a3-audio/a3-system/a3mix/python/mic.py

# This file is a part of A³Pandemic. License is GPLv3: https://github.com/ambisonics-audio-association/Ambijockey/blob/main/COPYING
# © Copyright 2021-2022 Patric Schmitz, Raphael Eismann, Jendrik Bradaczek
#!/usr/bin/python

import sys
import math
import time
import argparse
import serial  # pySerial https://pyserial.readthedocs.io/
import numpy as np

import board
import neopixel

from multiprocessing import Process

from pythonosc.udp_client import SimpleUDPClient
from pythonosc import osc_server
from pythonosc import dispatcher

from typing import List, Any

pixel_pin = board.D18
num_pixels = 10

ORDER = neopixel.GRB

pixels = neopixel.NeoPixel(
    pixel_pin, num_pixels, brightness=0.1, auto_write=False, pixel_order=ORDER
)

pixel_fx_mode_highpass = 8
pixel_fx_mode_lowpass = 9

pixels_fx_toggle = [0, 2, 4, 6]
pixels_3d_toggle = [1, 3, 5, 7]

color_led_on = (255,255,255)
color_led_off = (0,0,0)

def pixel_color(r,g,b):
    pixels.fill((r,g,b))
    pixels.show()

fx_state = np.zeros(10)

# OSC-Clients
osc_core = SimpleUDPClient('192.168.43.50', 9000)

# OSC-Server
osc_vu_receive_port = 7771

vu_channel_to_led_count = {
    0 : 8,
    1 : 8,
    2 : 8,
    3 : 8,
    4 : 32,
    5 : 32,
    6 : 32,
    7 : 32,
    8 : 32,
    9 : 32,
    10 : 32,
    11 : 32,
}

# channel strips 1-4
analog_pots_per_channel_to_osc_param = {
    "0": "gain",
    "1": "eq/high",
    "2": "eq/mid",
    "3": "eq/low",
    "4": "volume",
    "5": "fx-send",
}

button_per_channel_to_osc_param = {
    "0": "pfl",
    "1": "fx",
    "2": "3d",
}

button_fx_to_mode_name = {
    "0": "high_pass",
    "1": "low_pass",
}

# master section pots mapping
master_pots_to_osc_message = {
    "0": "/master/volume",
    "1": "/fx/frequency",
    "2": "/fx/resonance",
    "3": "/master/booth",
    "4": "/master/phones_mix",
    "5": "/master/phones_volume",
}

last_used_enc = 0

# time_last_receive = 0

def db_value_to_index(value: float, num_leds: int):
    index = int(np.interp(value, [-60, 0], [0, num_leds]))
    if index == num_leds:
        index = num_leds - 1
    return index

def send_vu_data(vu: str, peak_db: float, rms_db: float):
    num_leds = vu_channel_to_led_count[int(vu)]
    peak_index = db_value_to_index(peak_db, num_leds)
    rms_index = db_value_to_index(rms_db, num_leds)

#    print("peak: " + str(peak_db) + " " + str(peak_index))
#    print("rms: " + str(rms_db) + " " + str(rms_index))

    sendData("VU:" + vu + ":" + str(peak_index) + ":" + str(rms_index))

def vu_handler(address: str,
               *osc_arguments: List[Any]) -> None:
    words = address.split("/")
    vu = words[2]

    peak = osc_arguments[0]
    rms = osc_arguments[1]

    # clamp to above 0 to avoid numerical error
    if peak == 0.0:
        peak = sys.float_info.epsilon
    if rms == 0.0:
        rms = sys.float_info.epsilon

    peak_db = 20 * math.log(peak, 10)
    rms_db  = 20 * math.log(rms, 10)

    send_vu_data(vu, peak_db, rms_db)


def send_pfl_leds_data(channel: str, pfl_led_on: int):
    message = "LED:" + str(channel) + ":" + str(pfl_led_on)
    sendData(message)
#    print(message)

def led_handler_channel(address: str,
                        *osc_arguments: List[Any]) -> None:
#    print(f'led_handler_channel: {address}')

    words = address.split("/")
    channel = words[2]
    led_type = words[4]
    led_on = int(osc_arguments[0])

#    print(f'toggling {led_type} led for channel {channel}: {led_on}')

    if led_type == "pfl":
        send_pfl_leds_data(channel, led_on)
    elif led_type == "fx":
        pixels[pixels_fx_toggle[int(channel)]] = color_led_on if led_on else color_led_off
        pixels.show()
    elif led_type == "3d":
        pixels[pixels_3d_toggle[int(channel)]] = color_led_on if led_on else color_led_off
        pixels.show()


def led_handler_fx(address: str,
                   *osc_arguments: List[Any]) -> None:
#    print(f'led_handler_fx: {address}')

    led_fx_mode = osc_arguments[0]

    if led_fx_mode not in ["high_pass", "low_pass"]:
        return

    high_pass = led_fx_mode == "high_pass"

    pixels[pixel_fx_mode_highpass] = color_led_on if high_pass else color_led_off
    pixels[pixel_fx_mode_lowpass] = color_led_off if high_pass else color_led_on
    pixels.show()


def tap_handler(address: str,
               *osc_arguments: List[Any]) -> None:
    words = address.split("/")
    tap = words[1]

    value = osc_arguments[0]

    message = "TAP:" + str(value)
    sendData(message)
    print(message)

# Serial communication
#ser = serial.Serial('/dev/ttyACM0', 115200)
ser = serial.Serial('/dev/ttyACM0', 4608000)
ser.flush()

def sendData(data): # send Serial data
    data += "\r\n"
    ser.write(data.encode())

def serial_handler(): # dispatch from serial stream and send to osc

    while True:
        line = ser.readline().decode('utf-8').rstrip()

        # global time_last_receive
        # current_time_ns = time.clock_gettime_ns(time.CLOCK_REALTIME)
        # delta_time_ms = (current_time_ns - time_last_receive)/1e6
        # if delta_time_ms < 10:
        #     continue
        # print(f'time delta: {delta_time_ms}')
        # time_last_receive = current_time_ns

#        print(line)

        words = line.split(":")

        track = words[1]
        mode = words[2]
        index = words[3]
        value = words[4]

#        print(f'value: {value}')

        # Buttons
        if mode == "B":
            # the 4 channel strips
            channel_names = map(str, range(5))
            if track in channel_names:
                osc_core.send_message("/channel/" + track + "/" +
                                      button_per_channel_to_osc_param[index], value)
            elif track == "fx" and value == "1":
                osc_core.send_message("/fx/mode", button_fx_to_mode_name[index])

        if mode == "TAP":
            osc_core.send_message("/tap", value)

        if mode == "EB": # Encoder Button
                osc_core.send_message("/channel/" + track + "/encbtn", value)

        if mode == "ENC": # Encoder
                osc_core.send_message("/channel/" + track + "/enc", value)
                global last_used_enc
                if track != last_used_enc:
                    last_used_enc = track
        
        # Potis
        if mode == "P":
            # the 4 channel strips
            channel_names = map(str, range(4))
            if track in channel_names:
                if index in analog_pots_per_channel_to_osc_param:
                    osc_core.send_message("/channel/" + track + "/" +
                                            analog_pots_per_channel_to_osc_param[index], value)

            # pots in the master section
            elif track == "master":
                if index in master_pots_to_osc_message:
                    osc_core.send_message(master_pots_to_osc_message[index], value)


if __name__ == '__main__':

    proc1 = Process(target=serial_handler)
    proc1.start()

    parser = argparse.ArgumentParser()
    parser.add_argument("--ip", default="0.0.0.0", help="The ip to listen on for VU meter messages")
    parser.add_argument("--port", type=int,
                        default=osc_vu_receive_port, help="The port to listen on for VU meter messages")
    args = parser.parse_args()

    dispatcher = dispatcher.Dispatcher()
    dispatcher.map("/vu/*", vu_handler)
    dispatcher.map("/channel/*/led/*", led_handler_channel)
    dispatcher.map("/fx/led", led_handler_fx)
    #dispatcher.map("/clock", tap_handler)

    server = osc_server.BlockingOSCUDPServer((args.ip, args.port), dispatcher)
#    print("Serving on {}".format(server.server_address))
    server.serve_forever()
