a3-audio/a3-system/a3motion/raspberry/boot/config.txt

# See /boot/overlays/README for all available options

dtoverlay=vc4-kms-v3d
initramfs initramfs-linux.img followkernel

display_rotate=2
# device_tree_param=spi=on
# dtparam=i2c_arm=on
# disable_splash=1
