a3-audio/a3-system/a3motion/mocCode/mocFullTest.X/src/encoderAlternative.h

/* 
 * File:   encoderAlternative.h
 * Author: tiri
 *
 * Created on April 1, 2023, 2:10 PM
 */

#ifndef ENCODERALTERNATIVE_H
#define	ENCODERALTERNATIVE_H
#include "hardware.h"
#include "bitoperation.h"
#include <avr/interrupt.h>
void enc_init(uint8_t enc_step);
void enc_update();
void enc_set_step(uint8_t step);
int8_t enc_getValue();

#endif	/* ENCODERALTERNATIVE_H */
