a3-audio/a3-system/a3motion/mocCode/mocFullTest.X/src/debug.h

/*
 * debug.h
 *
 * Created: 18/03/2022 10:25:53
 *  Author: tirii
 */ 


#ifndef DEBUG1_H_
#define DEBUG1_H_
#include <avr/io.h>
#include "hardware.h"
#include "bitoperation.h"
extern void toggleCh1();
extern void toggleCh2();

#endif /* DEBUG_H_ */
