a3-audio/a3-system/a3motion/mocCode/mocFullTest.X/includes.h

/*
 * includes.h
 *
 * Created: 22/03/2022 14:41:26
 *  Author: tirii
 */ 


#ifndef INCLUDES_H_
#define INCLUDES_H_
//#include <stdlib.h>
//#include <string.h>
//#include <math.h>
//#include <avr/io.h>
//#include <avr/cpufunc.h> /* Required header file */
//#include <avr/interrupt.h>
//#include <avr/pgmspace.h>
//#include	<stdbool.h>


#endif /* INCLUDES_H_ */
