a3-audio/a3-system/a3motion/mocCode/mocFullTest.X/src/timer.h

/*
 * timer.h
 *
 * Created: 22/03/2022 15:18:33
 *  Author: tirii
 */ 


#ifndef TIMER_H_
#define TIMER_H_
#include "hardware.h"
#include <avr/io.h>
void time_t0Init();
void time_t1Init();



#endif /* TIMER_H_ */
